lfc7/TAP-tempo-LFO/customChar.h

byte blanche[8] = {
  0b00000,
  0b00100,
  0b00100,
  0b00100,
  0b00100,
  0b11100,
  0b10100,
  0b11100
};

byte noire[8] = {
  0b00000,
  0b00100,
  0b00100,
  0b00100,
  0b00100,
  0b11100,
  0b11100,
  0b11100
};

byte croche[8] = {
  0b00000,
  0b00110,
  0b00101,
  0b00101,
  0b00100,
  0b11100,
  0b11100,
  0b11100
};

byte dblcroche[8] = {
  0b00110,
  0b00101,
  0b00101,
  0b00110,
  0b00101,
  0b11101,
  0b11100,
  0b11100
};

byte triolet[8] = {
  0b00111,
  0b00001,
  0b00011,
  0b00001,
  0b00111,
  0b00000,
  0b00000,
  0b00000
};


uint8_t noteChar[][2] = {
  {0,32},
  {0,4},
  {1,32},
  {1,4},
  {2,32},
  {2,4},
  {3,32},
  {3,4},
  {3,3},
  {3,3}
};
